nsdesai/dynamic_clamp/dynamic_clamp/HCN.ino

// H current from model in Vaidya and Johnston, Nat. Neurosci. (2013).
// For speed, the parameters sinf and tau are pre-calculated for a wide range of Vm
// and put in lookup tables stored as global variables.

// Declare the lookup table variables
float sinf1[1501] = {0.0};                                    // Pre-calculate the activation parameters for
float tau1[1501] = {0.0};                                     // HCN currents: Vm from -100 mV to +50 mV in
                                                              // steps of 0.1 mV
// Generate the lookup tables
void GenerateHcnLUT() {
  float v;
  for (int x=0; x<1501; x++) {
    v = (float)x/10 - 100;
    sinf1[x] = 1/(1 + expf((v+82.0)/8)); 
    tau1[x] = 10*expf(.033*(v+75))/(0.11*(1+expf(0.083*(v+75)))); 
  }
}

// At every time step, calculate the HCN current in the Hodgkin-Huxley manner
float HCN(float v, float gH) {
  static float sVar = 0.0;                                    // initialize activation gate, executed once
  if (gH==0.0) {
    sVar = 0.0;                                               // reset activation gate before next run
    return 0.0;
  } else {
    float v10 = v*10.0;
    int vIdx = (int)v10 + 1000;
    vIdx = constrain(vIdx,0,1500);
    sVar = sVar + dt * ( -(sVar-sinf1[vIdx])/tau1[vIdx] );      // forward Euler method
    if (sVar<0.0) sVar=0.0;                                     // non-negative only
    float current = -gH * sVar * (v + 30);                      // injected current (pA) 
    return current;
  }
}
